Elecrow-RD/CrowPanel-ESP32-2.9-E-paper-HMI-Display-with-128-296/factory_sourecode/2.9_tow/pic/NEW_UI_2-9_BW_02/NEW_UI_2-9_BW_02/NEW_UI_2-9_BW_Product-Description-01.bmp

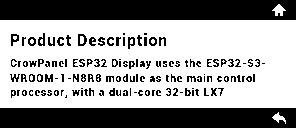
factory_sourecode/2.9_tow/pic/NEW_UI_2-9_BW_02/NEW_UI_2-9_BW_02/NEW_UI_2-9_BW_Product-Description-01.bmp
