Elecrow-RD/CrowPanel-ESP32-2.9-E-paper-HMI-Display-with-128-296/factory_sourecode/2.9_tow/pic/ui_2-9_202406_02/UI_2_9_202406_Product-Description-02.bmp

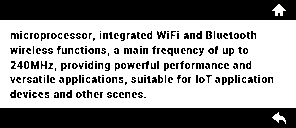
factory_sourecode/2.9_tow/pic/ui_2-9_202406_02/UI_2_9_202406_Product-Description-02.bmp
