Elecrow-RD/CrowPanel-ESP32-2.9-E-paper-HMI-Display-with-128-296/factory_sourecode/2.9_tow/main/pic_image.h

const unsigned char gImage_image[4736] = { /* 0X00,0X01,0X28,0X01,0X80,0X00, */
0X00,0X00,0X00,0X00,0X00,0X00,0X00,0X01,0X80,0X00,0X00,0X00,0X07,0X00,0X00,0X00,
0X00,0X00,0X00,0X0C,0X00,0X00,0X00,0X00,0X00,0X00,0X00,0X00,0X00,0X00,0X10,0X03,
0X80,0X00,0X00,0X20,0X00,0X00,0X00,0X00,0X00,0X00,0X00,0X00,0X00,0X80,0X00,0X00,
0X00,0X01,0X80,0X00,0X00,0X00,0X00,0X00,0X0C,0X00,0X00,0X00,0X00,0X00,0X00,0X00,
0X00,0X00,0X00,0X10,0X01,0X80,0X00,0X00,0X20,0X00,0X00,0X00,0X00,0X00,0X00,0X00,
0X00,0X00,0XC0,0X00,0X00,0X00,0X00,0XC0,0X00,0X00,0X00,0X00,0X00,0X0C,0X00,0X00,
0X00,0X00,0X00,0X00,0X00,0X00,0X00,0X00,0X00,0X00,0XC1,0XF8,0X00,0X20,0X00,0X00,
0X00,0X00,0X00,0X00,0X00,0X00,0X00,0X40,0X00,0X00,0X00,0X00,0X60,0X00,0X00,0X00,
0X00,0X00,0X0C,0X7E,0X00,0X00,0X00,0X00,0X00,0X00,0X00,0X00,0X00,0X00,0X00,0X6F,
0XFE,0X00,0X20,0X00,0X00,0X00,0X00,0X00,0X00,0X00,0X00,0X00,0X60,0X00,0X00,0X00,
0X00,0X30,0X00,0X00,0X00,0X00,0X00,0X0F,0XFF,0XE0,0X00,0X00,0X00,0X00,0X00,0X00,
0X00,0X00,0X00,0X00,0X38,0X03,0X87,0XE0,0X00,0X00,0X00,0X00,0X00,0X00,0X00,0X00,
0X00,0X60,0X00,0X00,0X00,0X00,0X18,0X00,0X00,0X00,0X00,0X00,0X0F,0X00,0X78,0X00,
0X00,0X00,0X00,0X00,0X00,0X00,0X00,0X00,0X00,0X30,0X00,0XFF,0XE0,0X00,0X00,0X00,
0X00,0X00,0X00,0X00,0X00,0X00,0X60,0X00,0X00,0X00,0X00,0X08,0X00,0X00,0X00,0X00,
0X00,0X0C,0X00,0X0E,0X00,0X00,0X00,0X00,0X00,0X00,0X00,0X00,0X00,0X00,0X10,0X00,
0X30,0X00,0X00,0X00,0X00,0X00,0X00,0X00,0X00,0X00,0X00,0X20,0XFC,0X00,0X00,0X00,
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
0X00,0X00,0X80,0X00,0X00,0X00,0X00,0X00,0X00,0X00,0X00,0X00,0X00,0X00,0X00,0X00,
0X00,0X00,0X00,0X00,0X00,0X00,0X00,0X00,0X00,0X00,0X00,0X00,0X00,0XFE,0XF0,0X00,
0XFC,0X00,0X30,0X00,0X18,0X00,0X00,0X80,0X00,0X00,0X00,0X00,0X00,0X00,0X00,0X00,
0X00,0X00,0X00,0X00,0X00,0X00,0X00,0X00,0X00,0X00,0X00,0X00,0X00,0X00,0X00,0X00,
0X00,0X00,0X00,0X70,0X00,0X1E,0X00,0X38,0X00,0X18,0X00,0X00,0X80,0X00,0X00,0X00,
0X00,0X00,0X00,0X00,0X00,0X00,0X00,0X00,0X00,0X00,0X00,0X00,0X00,0X00,0X00,0X00,
0X00,0X00,0X00,0X00,0X00,0X00,0X00,0X00,0X00,0X00,0X07,0X80,0X18,0X00,0X1C,0X00,
0X01,0X80,0X00,0X00,0X00,0X00,0X00,0X00,0X00,0X00,0X00,0X00,0X00,0X00,0X00,0X00,
0X00,0X00,0X00,0X00,0X00,0X00,0X00,0X00,0X00,0X00,0X00,0X00,0X00,0X00,0X00,0X01,
0XE0,0X1C,0X00,0X0C,0X00,0X01,0X80,0X00,0X00,0X00,0X00,0X00,0X00,0X00,0X00,0X00,
};
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
