Elecrow-RD/CrowPanel-ESP32-2.9-E-paper-HMI-Display-with-128-296/example/arduino/Demos/2.9_WIFI_refresh/Ap_29demo.h

const unsigned char gImage_Num[10][32] = {
  //0
  { /* 0X00,0X01,0X10,0X00,0X10,0X00, */
    0X00, 0X00, 0X0F, 0XC0, 0X0F, 0XE0, 0X1C, 0X70, 0X18, 0X70, 0X18, 0X70, 0X38, 0X70, 0X38, 0X70,
    0X38, 0X70, 0X38, 0X70, 0X18, 0X70, 0X1C, 0X70, 0X1C, 0X70, 0X0F, 0XE0, 0X07, 0XC0, 0X00, 0X00,
  },
  //1
  { /* 0X00,0X01,0X10,0X00,0X10,0X00, */
    0X00, 0X00, 0X00, 0XE0, 0X07, 0XE0, 0X0F, 0XE0, 0X0C, 0XE0, 0X00, 0XE0, 0X00, 0XE0, 0X00, 0XE0,
    0X00, 0XE0, 0X00, 0XE0, 0X00, 0XE0, 0X00, 0XE0, 0X00, 0XE0, 0X00, 0XE0, 0X00, 0XE0, 0X00, 0X00,
  },
  //2
  { /* 0X00,0X01,0X10,0X00,0X10,0X00, */
    0X00, 0X00, 0X0F, 0XC0, 0X1F, 0XE0, 0X38, 0XF0, 0X38, 0X70, 0X00, 0X70, 0X00, 0XE0, 0X00, 0XE0,
    0X01, 0XC0, 0X03, 0X80, 0X07, 0X00, 0X0E, 0X00, 0X1C, 0X00, 0X3F, 0XF0, 0X3F, 0XF0, 0X00, 0X00,
  },
  //3
  { /* 0X00,0X01,0X10,0X00,0X10,0X00, */
    0X00, 0X00, 0X0F, 0XE0, 0X1F, 0XE0, 0X1C, 0X70, 0X18, 0X70, 0X00, 0X70, 0X00, 0XE0, 0X07, 0XE0,
    0X07, 0XE0, 0X00, 0X70, 0X00, 0X70, 0X18, 0X70, 0X1C, 0X70, 0X1F, 0XE0, 0X0F, 0XE0, 0X00, 0X00,
  },
  //4
  { /* 0X00,0X01,0X10,0X00,0X10,0X00, */
    0X00, 0X00, 0X00, 0XF0, 0X00, 0XF0, 0X01, 0XF0, 0X03, 0XF0, 0X03, 0XF0, 0X07, 0X70, 0X0E, 0X70,
    0X0C, 0X70, 0X1C, 0X70, 0X1F, 0XF8, 0X3F, 0XF8, 0X00, 0X70, 0X00, 0X70, 0X00, 0X70, 0X00, 0X00,
  },
  //5
  { /* 0X00,0X01,0X10,0X00,0X10,0X00, */
    0X00, 0X00, 0X0F, 0XF0, 0X0F, 0XF0, 0X0C, 0X00, 0X1C, 0X00, 0X1C, 0X00, 0X1F, 0XE0, 0X1F, 0XE0,
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
  0X00, 0X00, 0X00, 0X00, 0X00, 0X00, 0X00, 0X00, 0X00, 0X00, 0X00, 0X00, 0X00, 0X00, 0X00, 0X00,
  0X00, 0X00, 0X00, 0X00, 0X00, 0X00, 0X00, 0X00, 0X00, 0X00, 0X00, 0X00, 0X00, 0X00, 0X00, 0X00,
  0X00, 0X00, 0X00, 0X00, 0X00, 0X00, 0X00, 0X00, 0X00, 0X00, 0X00, 0X00, 0X00, 0X00, 0X00, 0X00,
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
